pmarches/heater-load-wifi/heater-load-wifi/settings_html.c

unsigned char settings_html[] = {
  0x3c, 0x21, 0x44, 0x4f, 0x43, 0x54, 0x59, 0x50, 0x45, 0x20, 0x68, 0x74,
  0x6d, 0x6c, 0x3e, 0x0a, 0x3c, 0x48, 0x54, 0x4d, 0x4c, 0x20, 0x6c, 0x61,
  0x6e, 0x67, 0x3d, 0x22, 0x65, 0x6e, 0x22, 0x3e, 0x0a, 0x3c, 0x73, 0x63,
  0x72, 0x69, 0x70, 0x74, 0x3e, 0x0a, 0x0a, 0x66, 0x75, 0x6e, 0x63, 0x74,
  0x69, 0x6f, 0x6e, 0x20, 0x73, 0x61, 0x76, 0x65, 0x53, 0x65, 0x74, 0x74,
  0x69, 0x6e, 0x67, 0x73, 0x28, 0x29, 0x7b, 0x0a, 0x20, 0x20, 0x20, 0x20,
  0x76, 0x61, 0x72, 0x20, 0x78, 0x6d, 0x6c, 0x68, 0x74, 0x74, 0x70, 0x20,
  0x3d, 0x20, 0x6e, 0x65, 0x77, 0x20, 0x58, 0x4d, 0x4c, 0x48, 0x74, 0x74,
  0x70, 0x52, 0x65, 0x71, 0x75, 0x65, 0x73, 0x74, 0x28, 0x29, 0x3b, 0x0a,
  0x20, 0x20, 0x20, 0x20, 0x76, 0x61, 0x72, 0x20, 0x73, 0x65, 0x74, 0x74,
  0x69, 0x6e, 0x67, 0x73, 0x5f, 0x66, 0x6f, 0x72, 0x6d, 0x20, 0x3d, 0x20,
  0x64, 0x6f, 0x63, 0x75, 0x6d, 0x65, 0x6e, 0x74, 0x2e, 0x67, 0x65, 0x74,
  0x45, 0x6c, 0x65, 0x6d, 0x65, 0x6e, 0x74, 0x42, 0x79, 0x49, 0x64, 0x28,
  0x27, 0x73, 0x65, 0x74, 0x74, 0x69, 0x6e, 0x67, 0x73, 0x5f, 0x66, 0x6f,
  0x72, 0x6d, 0x27, 0x29, 0x3b, 0x0a, 0x20, 0x20, 0x20, 0x20, 0x76, 0x61,
  0x72, 0x20, 0x66, 0x6f, 0x72, 0x6d, 0x44, 0x61, 0x74, 0x61, 0x20, 0x3d,
  0x20, 0x6e, 0x65, 0x77, 0x20, 0x46, 0x6f, 0x72, 0x6d, 0x44, 0x61, 0x74,
  0x61, 0x28, 0x73, 0x65, 0x74, 0x74, 0x69, 0x6e, 0x67, 0x73, 0x5f, 0x66,
  0x6f, 0x72, 0x6d, 0x29, 0x3b, 0x0a, 0x20, 0x20, 0x20, 0x20, 0x76, 0x61,
  0x72, 0x20, 0x6a, 0x73, 0x6f, 0x6e, 0x54, 0x6f, 0x53, 0x65, 0x6e, 0x64,
  0x3d, 0x4a, 0x53, 0x4f, 0x4e, 0x2e, 0x73, 0x74, 0x72, 0x69, 0x6e, 0x67,
  0x69, 0x66, 0x79, 0x28, 0x4f, 0x62, 0x6a, 0x65, 0x63, 0x74, 0x2e, 0x66,
  0x72, 0x6f, 0x6d, 0x45, 0x6e, 0x74, 0x72, 0x69, 0x65, 0x73, 0x28, 0x66,
  0x6f, 0x72, 0x6d, 0x44, 0x61, 0x74, 0x61, 0x29, 0x29, 0x3b, 0x0a, 0x0a,
  0x20, 0x20, 0x20, 0x20, 0x78, 0x6d, 0x6c, 0x68, 0x74, 0x74, 0x70, 0x2e,
  0x6f, 0x70, 0x65, 0x6e, 0x28, 0x22, 0x50, 0x4f, 0x53, 0x54, 0x22, 0x2c,
  0x20, 0x22, 0x2f, 0x73, 0x74, 0x61, 0x74, 0x65, 0x22, 0x2c, 0x20, 0x74,
  0x72, 0x75, 0x65, 0x29, 0x3b, 0x0a, 0x20, 0x20, 0x20, 0x20, 0x78, 0x6d,
  0x6c, 0x68, 0x74, 0x74, 0x70, 0x2e, 0x73, 0x65, 0x74, 0x52, 0x65, 0x71,
  0x75, 0x65, 0x73, 0x74, 0x48, 0x65, 0x61, 0x64, 0x65, 0x72, 0x28, 0x22,
  0x43, 0x6f, 0x6e, 0x74, 0x65, 0x6e, 0x74, 0x2d, 0x54, 0x79, 0x70, 0x65,
  0x22, 0x2c, 0x20, 0x22, 0x61, 0x70, 0x70, 0x6c, 0x69, 0x63, 0x61, 0x74,
  0x69, 0x6f, 0x6e, 0x2f, 0x6a, 0x73, 0x6f, 0x6e, 0x22, 0x29, 0x3b, 0x0a,
  0x20, 0x20, 0x20, 0x20, 0x78, 0x6d, 0x6c, 0x68, 0x74, 0x74, 0x70, 0x2e,
  0x73, 0x65, 0x6e, 0x64, 0x28, 0x6a, 0x73, 0x6f, 0x6e, 0x54, 0x6f, 0x53,
  0x65, 0x6e, 0x64, 0x29, 0x3b, 0x0a, 0x7d, 0x0a, 0x0a, 0x66, 0x75, 0x6e,
  0x63, 0x74, 0x69, 0x6f, 0x6e, 0x20, 0x70, 0x6f, 0x70, 0x75, 0x6c, 0x61,
  0x74, 0x65, 0x46, 0x6f, 0x72, 0x6d, 0x44, 0x61, 0x74, 0x61, 0x46, 0x72,
  0x6f, 0x6d, 0x4a, 0x53, 0x4f, 0x4e, 0x28, 0x6a, 0x73, 0x6f, 0x6e, 0x53,
  0x74, 0x72, 0x69, 0x6e, 0x67, 0x29, 0x7b, 0x0a, 0x20, 0x20, 0x20, 0x20,
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
};
unsigned int settings_html_len = 2457;
